latteflow/Pipli/Firmware/data_parse/src/main.cpp

#include <Arduino.h>
#include <ArduinoJson.h>

void setup()
{
  // Initialize serial port
  Serial.begin(115200);

  // Allocate the JSON document
  JsonDocument doc;

  // JSON input string.
  const char *json = "{\"sensor\":\"gps\",\"time\":1351824120,\"data\":[48.756080,2.302038]}";

  // Deserialize the JSON document
  DeserializationError error = deserializeJson(doc, json);

  // Test if parsing succeeds.
  if (error)
  {
    Serial.print(F("deserializeJson() failed: "));
    Serial.println(error.f_str());
    return;
  }

  // Fetch values.
  //
  // Most of the time, you can rely on the implicit casts.
  // In other case, you can do doc["time"].as<long>();
  const char *sensor = doc["sensor"];
  long time = doc["time"];
  double latitude = doc["data"][0];
  double longitude = doc["data"][1];

  // Print values.
  Serial.println(sensor);
  Serial.println(time);
  Serial.println(latitude, 6);
  Serial.println(longitude, 6);
}

void loop()
{
  // not used in this example
}
